LStranc/WeatherStation/Server_Code/weatherstation/pictures/pictures/Pressure.jpg

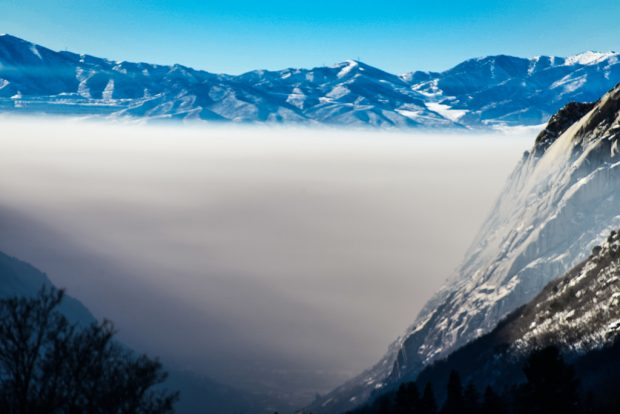
Server_Code/weatherstation/pictures/pictures/Pressure.jpg
