LStranc/WeatherStation/Server_Code/weatherstation/pictures/pictures/SLCDowntown.png

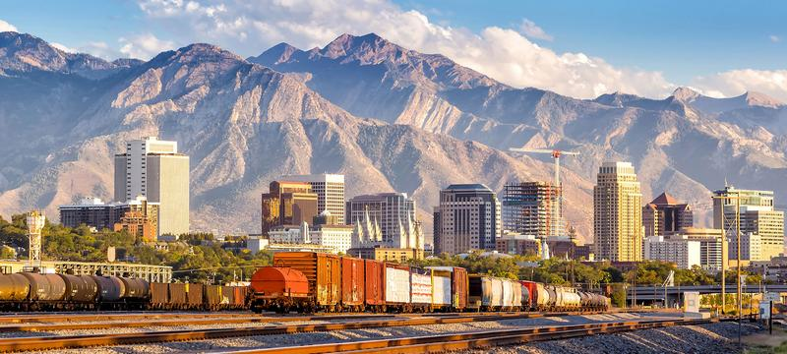
Server_Code/weatherstation/pictures/pictures/SLCDowntown.png
